uzairmahmed/ArduinoLightManager/Wiring/Perfboard_Wiring.png

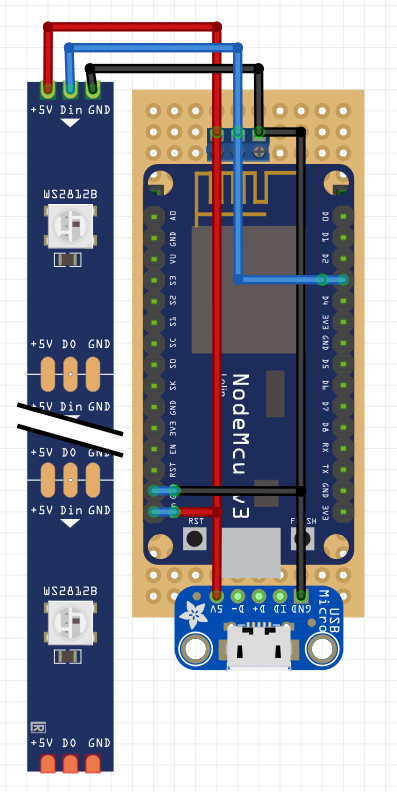
Wiring/Perfboard_Wiring.png
